vzlusat/vzlusat1-timepix-board/hardware/timepix_board/timepix_board_board_schematic.png

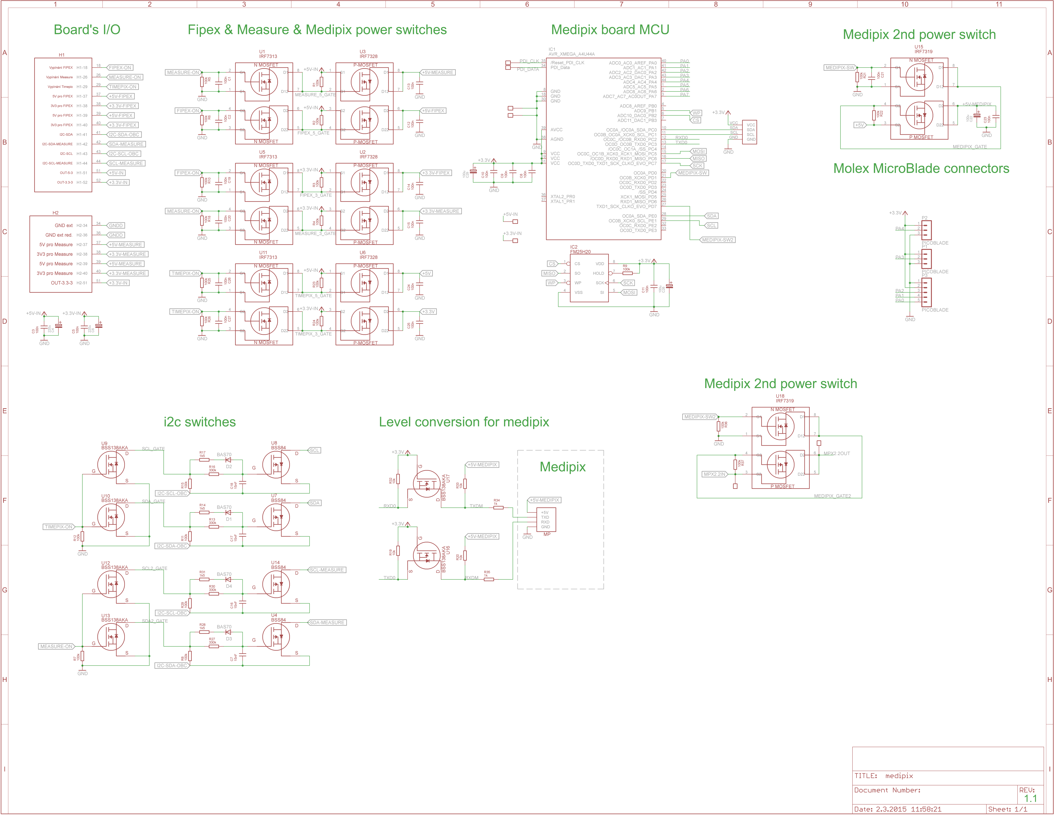
hardware/timepix_board/timepix_board_board_schematic.png
