vzlusat/vzlusat1-timepix-board/software/EqualizationParser/equalization_qualification_model/eqm.PNG

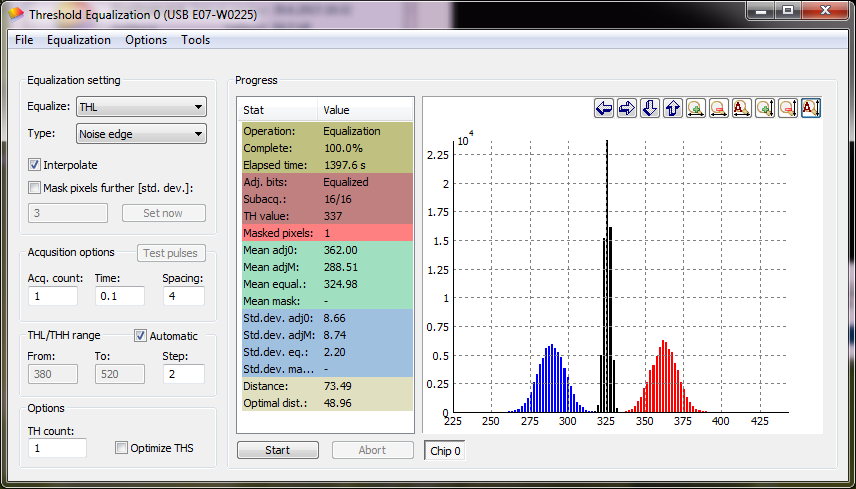
software/EqualizationParser/equalization_qualification_model/eqm.PNG
