vzlusat/vzlusat1-timepix-board/hardware/timepix_board/parts_top.png

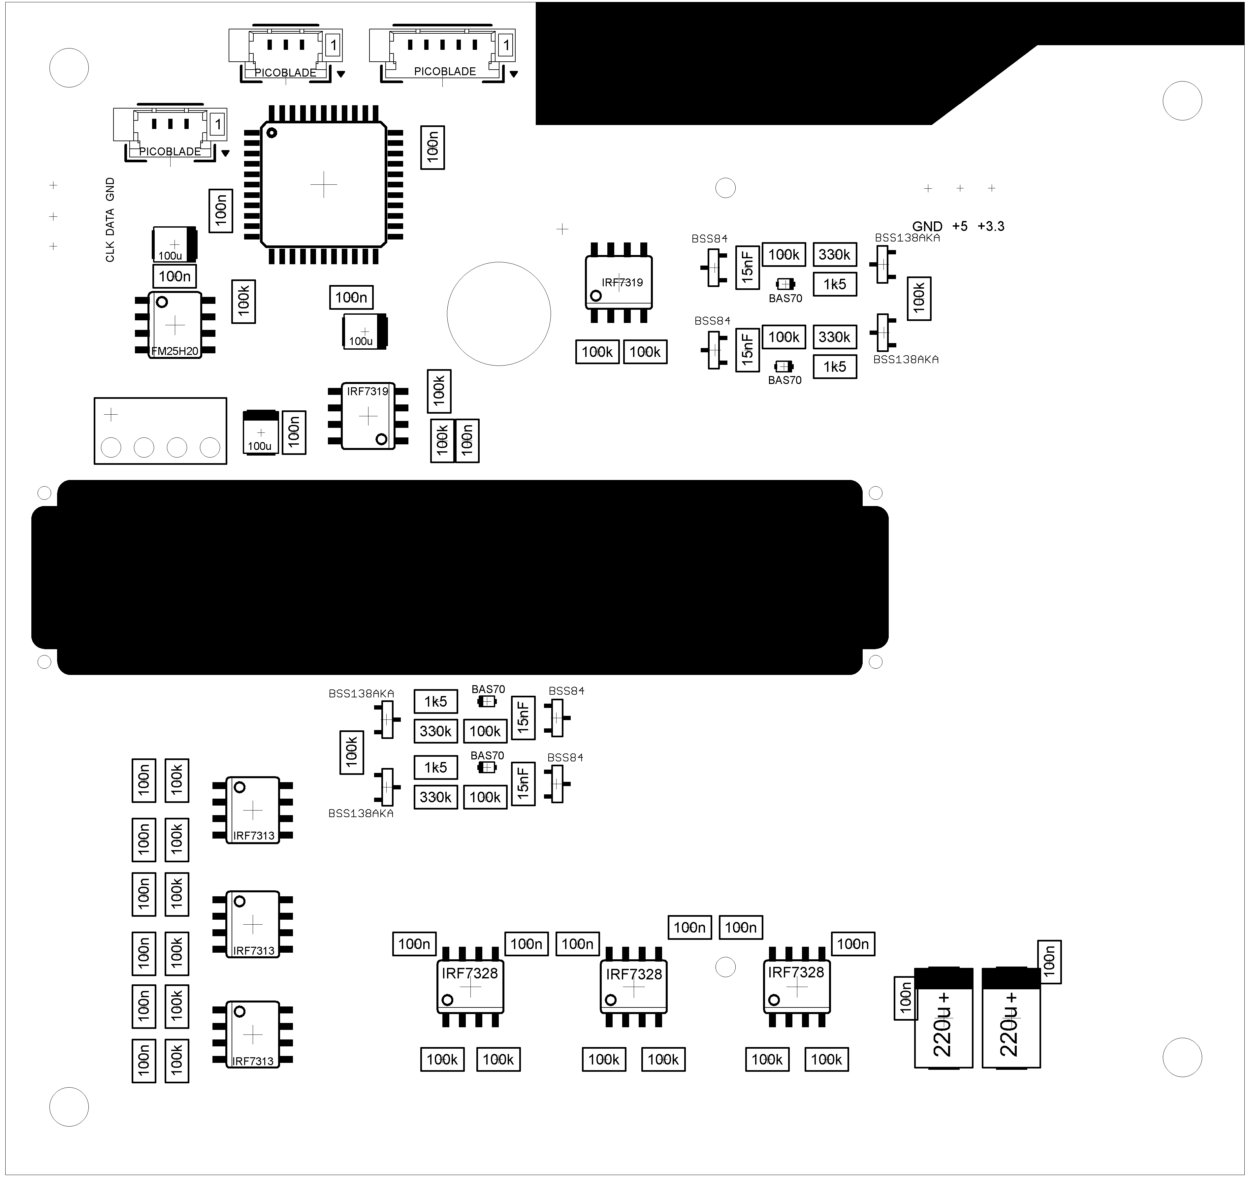
hardware/timepix_board/parts_top.png
