vzlusat/vzlusat1-timepix-board/measurements/13.7.2015_flight_model/s_optikou_vakuum/README.md

Měření 13.7.2015
================

Probíhalo měření s letovým HW a letovou optikou ve vakuu.

Legenda je uložena v mereni-13.7.2015-LETOVY.pdf

- Série měření s různou expozicí, se zaplou filtrací a v čítacím módu.
- Během měření se detektor ohřál a začal šumět, znatelné je to na snímcích 33 až 36, poté zníčení treshold z 430 na 420
- během poslední série měření byl výkon 40kV, 0.01mA, jinak všude 0.1mA
- ke snímkům jsou kromě jejich post-processované varianty ukládány i origiály

Konvence pojmenování souborů: soubor s "o" nakonci (např. image_513o.mat) obsahuje originální snímek, soubor s "f" (např. image_513f.mat) obsahuje snímek na nějž byla pouze aplikována filtrace, soubor s "p" nakonci (image_513p.mat) obsahuje příslušný zpracovaný snímek (tedy postprocess, filtrace, zmenšenina, podle toho, co bylo zapnuté).
