vzlusat/vzlusat1-timepix-board/measurements/13.7.2015_flight_model/srovnani_optika_ano_ne_vzduch/README.md

Měření 13.7.2015
================

Probíhalo měření s letovým HW v komoře v Rigaku. Máme dvě sady měření - (s optikou / bez optiky). Obojí na vzduchu.

Legenda je uložena v mereni-13.7.2015-LETOVY-SROVNANI-OPTIKA-ANO-NE.pdf
 
POZOR! Sada měření v režimu Time-Over-Treshold není validní pro srovnávání, v tuto dobu byla ještě přítomna chyba se zaokrouhlováním energie s hodnotou menší než 46 na nulu.

Všechna měření byla provedena s výkonem x-ray zdroje 40kV, 0.1mA a filtrace byla zaplá.

Ke všem měřením je přítomen i originální, nevyfiltrovaný snímek *_o.

Konvence pojmenování souborů: soubor s "o" nakonci (např. image_513o.mat) obsahuje originální snímek, soubor s "f" (např. image_513f.mat) obsahuje snímek na nějž byla pouze aplikována filtrace, soubor s "p" nakonci (image_513p.mat) obsahuje příslušný zpracovaný snímek (tedy postprocess, filtrace, zmenšenina, podle toho, co bylo zapnuté).
