vzlusat/vzlusat1-timepix-board/measurements/other_measurements/mereni_10.6.2015/README.md

Měření 10.6.2015
================

První "úspěšné" měření v komoře v Rigaku. Nicméně všechny snímky z tohoto měření nejsou použitelné pro jakékoliv srovnání. V této době byla špatně nahrávána equalizační matice, tedy treshold je zcela špatně a obrázek není kompletní. Vyčítání TOT režimu je také zkreslené zaokrouhlováním hodnot < 43 na nulu.
