vzlusat/vzlusat1-timepix-board/software/xMega_onboard_software/equalization_flight.c

/*
 * equalization.c
 * EQUALIZACE PRO LETOVY KUS
 */ 

#include "equalization.h"

#ifdef MEDIPIX_FLIGHT

#warning Flight Equalization used

#include <avr/pgmspace.h>

const uint8_t pseudoCount2high[8192] PROGMEM = {
	46,
	46,
	0,
	45,
	23,
	45,
	45,
	0,
	17,
	0,
	31,
	45,
	0,
	23,
	12,
	45,
	0,
	45,
	25,
	12,
	34,
	0,
	2,
	23,
	26,
	17,
	3,
	0,
	0,
	45,
	0,
	31,
	45,
	31,
	42,
	0,
	33,
	0,
	0,
	45,
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

const uint8_t pseudoCount2low[8192] PROGMEM = {
	21,
	8,
	0,
	251,
	244,
	238,
	56,
	0,
	123,
	0,
	218,
	43,
	0,
	231,
	31,
	225,
	0,
	212,
	33,
	18,
	169,
	0,
	118,
	218,
	46,
	110,
	185,
	0,
	0,
	30,
	0,
	205,
	165,
	192,
	149,
	0,
	64,
	0,
	0,
	17,
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

const uint8_t pseudoCount1high[8192] PROGMEM = {
	0,
	46,
	46,
	46,
	46,
	0,
	45,
	46,
	46,
	23,
	45,
	0,
	45,
	45,
	0,
	46,
	46,
	17,
	0,
	23,
	45,
	31,
	45,
	0,
	45,
	0,
	23,
	45,
	0,
	12,
	45,
	46,
	46,
	0,
	45,
	17,
	0,
	25,
	12,
	23,
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

const uint8_t pseudoCount1low[8192] PROGMEM = {
	0,
	22,
	9,
	23,
	10,
	0,
	252,
	24,
	11,
	245,
	239,
	0,
	253,
	57,
	0,
	25,
	12,
	124,
	0,
	246,
	240,
	219,
	44,
	0,
	254,
	0,
	232,
	58,
	0,
	32,
	226,
	26,
	13,
	0,
	213,
	125,
	0,
	34,
	19,
	247,
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

const uint8_t equalization8[8192] PROGMEM = {
39,
31,
47,
27,
39,
35,
43,
31,
27,
39,
35,
27,
35,
31,
35,
23,
43,
39,
35,
23,
39,
35,
31,
31,
23,
35,
43,
23,
31,
35,
35,
23,
31,
27,
27,
31,
31,
35,
43,
31,
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

const uint8_t equalization7[8192] PROGMEM = {
27,
31,
31,
35,
43,
31,
35,
31,
31,
35,
31,
35,
35,
35,
31,
35,
27,
27,
23,
27,
27,
27,
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
		0x590AB964, 0xAB613A67, 0xB831C993, 0x4A5A4A90, 0x9E902E7B, 0x6CFBAD78, 0x7FAB5E8C, 0x8DC0DD8F,
		0xE330A81A, 0x115B2B19, 0x020BD8ED, 0xF0605BEE, 0x24AA3F05, 0xD6C1BC06, 0xC5914FF2, 0x37FACCF1,
		0x69E9F0D5, 0x9B8273D6, 0x88D28022, 0x7AB90321, 0xAE7367CA, 0x5C18E4C9, 0x4F48173D, 0xBD23943E,
		0xF36E6F75, 0x0105EC76, 0x12551F82, 0xE03E9C81, 0x34F4F86A, 0xC69F7B69, 0xD5CF889D, 0x27A40B9E,
		0x79B737BA, 0x8BDCB4B9, 0x988C474D, 0x6AE7C44E, 0xBE2DA0A5, 0x4C4623A6, 0x5F16D052, 0xAD7D5351};

#endif
