vzlusat/vzlusat1-timepix-board/software/xMega_onboard_software/errorCodes.h

/*
 * errorCodes.h
 *
 * Created: 2.7.2015 18:48:39
 *  Author: klaxalk
 */ 


#ifndef ERRORCODES_H_
#define ERRORCODES_H_

#define ERROR_MEDIPIX_NOT_POWERED		'1'
#define ERROR_STORAGES_NOT_CREATED		'2'
#define ERROR_DATA_NOT_SAVED			'3'
#define ERROR_MEDIPIX_ALREADY_POWERED	'4'

#endif /* ERRORCODES_H_ */
